antmicro/job-storage-expansion/assets/wireframe/wireframe_dimensions.png

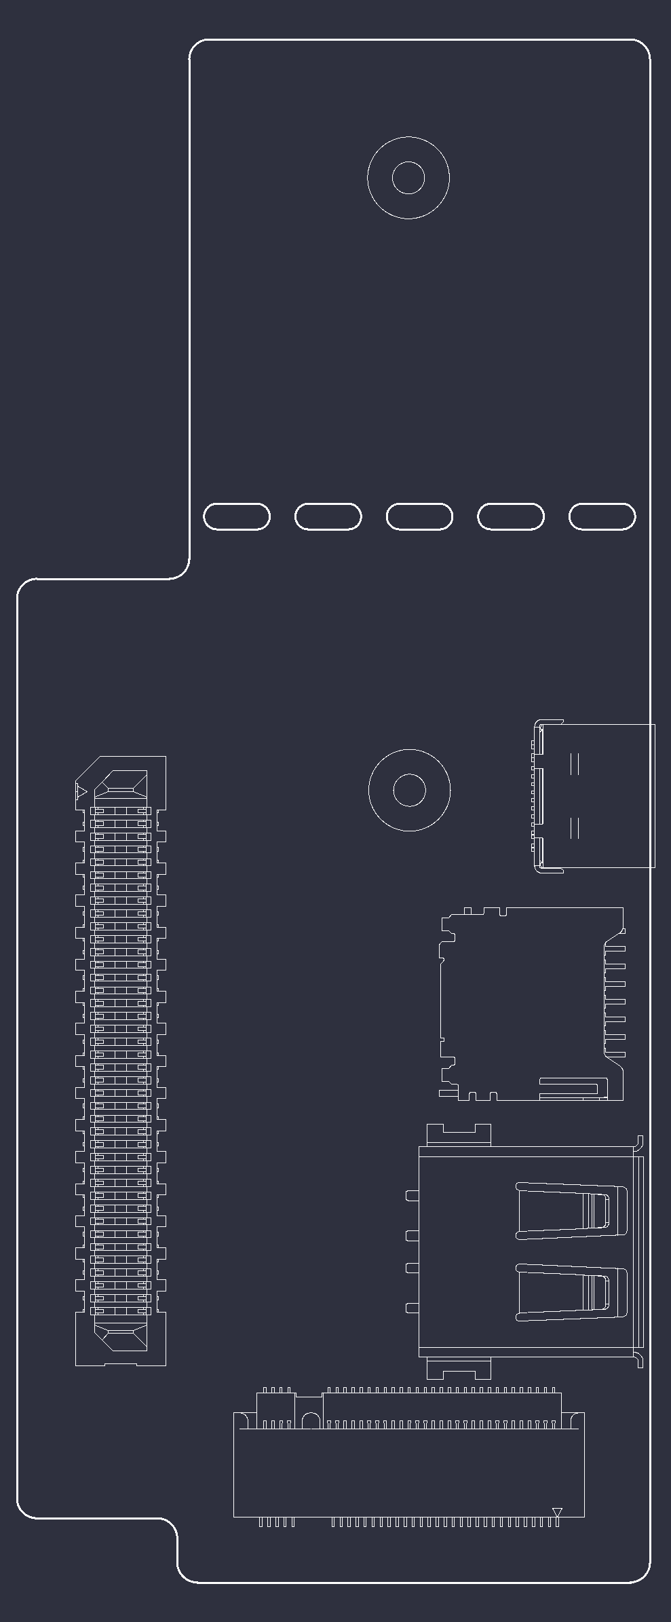
assets/wireframe/wireframe_dimensions.png
